8fb790dd/Raspberry_Cube/pics/RC1_running_4min_Screenshot from Screencast_27.10.2019_23:21:28.mp4.png

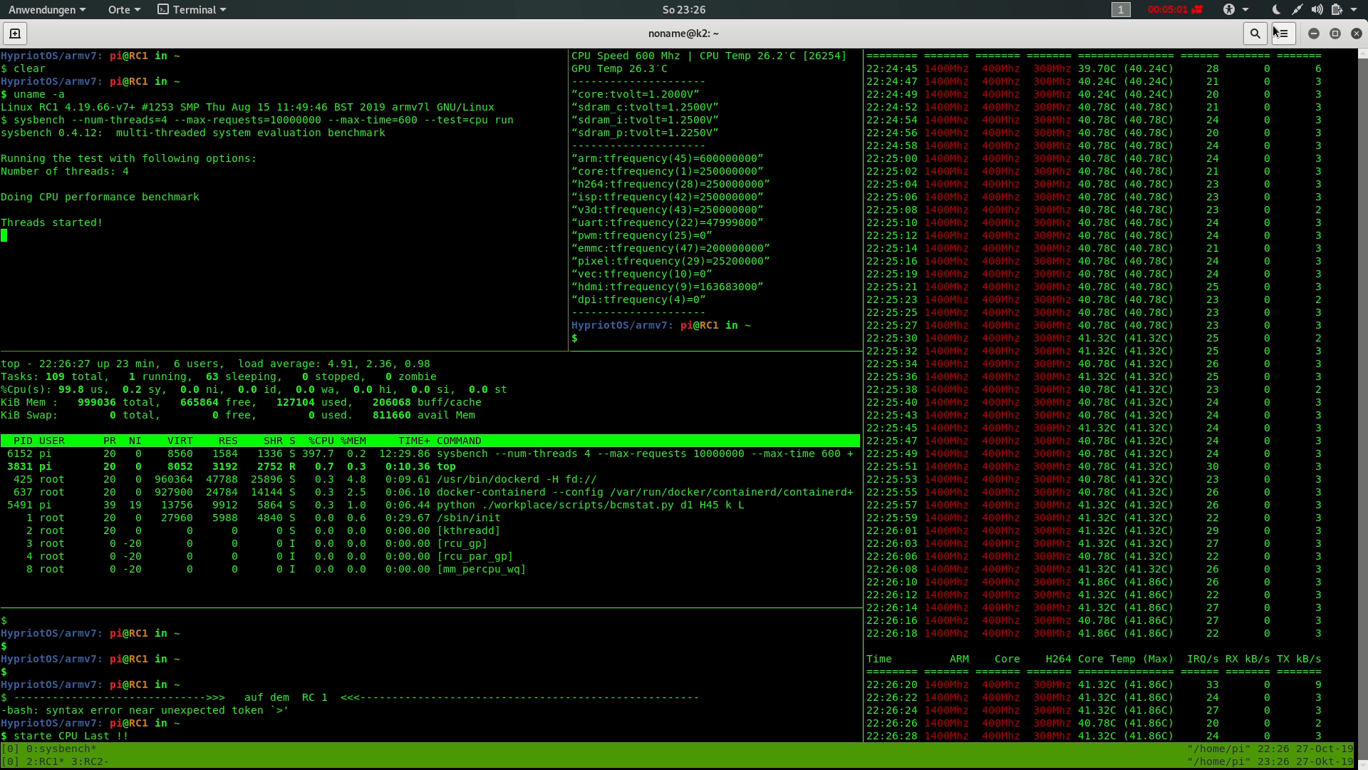
pics/RC1_running_4min_Screenshot from Screencast_27.10.2019_23:21:28.mp4.png
